osy/XG_Mobile_Station/Models/MX25L8006EM1I-12G.step

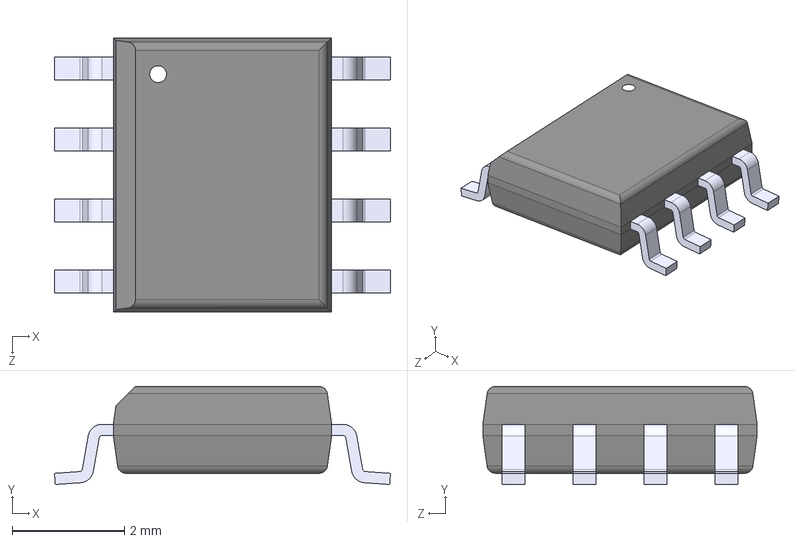
[picture p19: CAD file, 2024-03-20]
Models/MX25L8006EM1I-12G.step
6.00 x 1.75 x 4.90 mm
