osy/XG_Mobile_Station/Models/SN75LVPE4410RNQR.stp

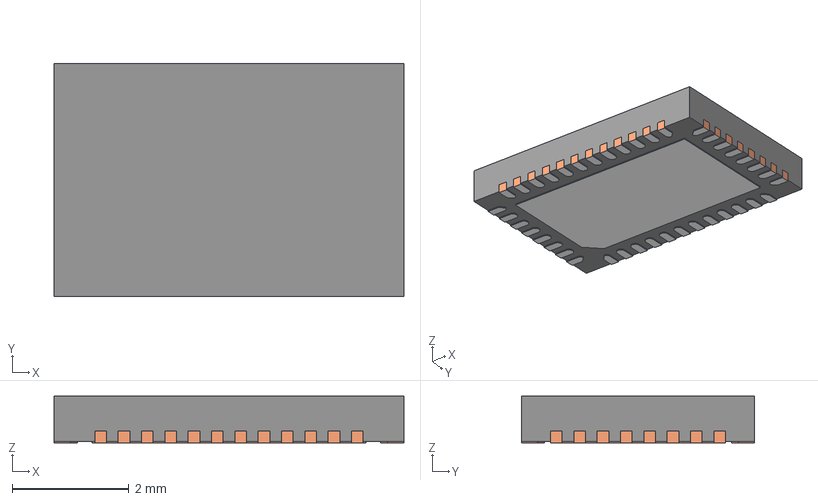
[picture p20: CAD file, 2024-03-20]
Models/SN75LVPE4410RNQR.stp
6.00 x 4.00 x 0.8 mm
BODY-QFN
FRAME-RNQ0040A
PIN1-ID
