osy/XG_Mobile_Station/Models/LM3489QMM-NOPB.stp

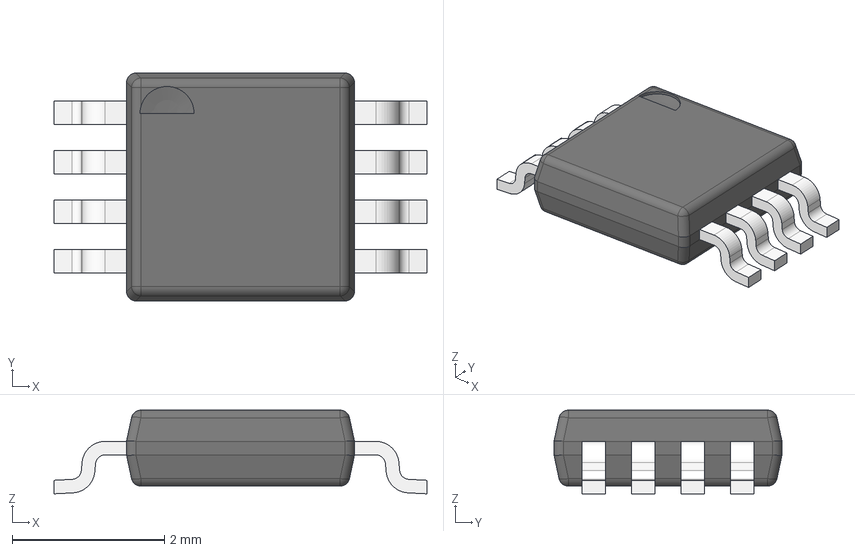
[picture p21: CAD file, 2024-03-20]
Models/LM3489QMM-NOPB.stp
4.90 x 3.00 x 1.10 mm
BODY_MUA08A
LEAD_MUA08A x 8
