osy/XG_Mobile_Station/Models/AON7403.step

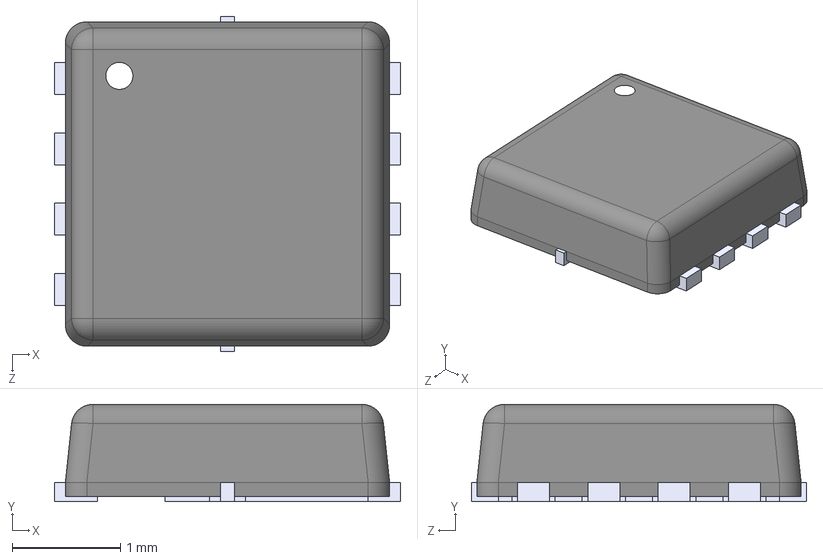
[picture p22: CAD file, 2024-03-20]
Models/AON7403.step
3.20 x 0.9 x 3.10 mm
