osy/XG_Mobile_Station/Models/LM3478MA-NOPB.stp

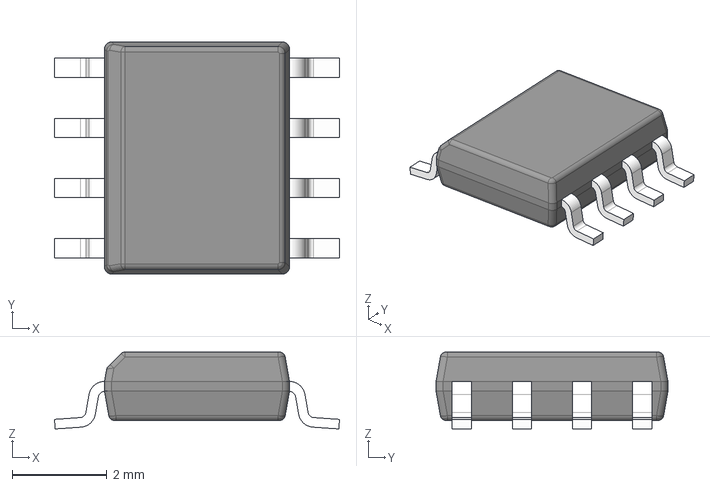
[picture p23: CAD file, 2024-03-20]
Models/LM3478MA-NOPB.stp
6.02 x 4.90 x 1.63 mm
BODY-SO
LEAD-D0008A x 8
