osy/XG_Mobile_Station/XGMDriver/devinstall/devinstall.h

/*++

Copyright (c) Microsoft Corporation.  All rights reserved.

Module Name:

    devcon.h

Abstract:

    Device Console header

--*/

#include <windows.h>
#include <tchar.h>
#include <stdlib.h>
#include <stdio.h>
#include <setupapi.h>
#include <regstr.h>
#include <infstr.h>
#include <cfgmgr32.h>
#include <string.h>
#include <malloc.h>
#include <newdev.h>
#include <objbase.h>
#include <strsafe.h>
#include <io.h>
#include <fcntl.h>

#include "msg.h"
#include "rc_ids.h"

#ifndef ARRAYSIZE
#define ARRAYSIZE(a)                (sizeof(a)/sizeof(a[0]))
#endif

typedef int (*DispatchFunc)(_In_ LPCTSTR BaseName, _In_opt_ LPCTSTR Machine, _In_ DWORD Flags, _In_ int argc, _In_ LPTSTR argv[]);
typedef int (*CallbackFunc)(_In_ HDEVINFO Devs, _In_ PSP_DEVINFO_DATA DevInfo, _In_ DWORD Index, _In_ LPVOID Context);

typedef struct {
    LPCTSTR         cmd;
    DispatchFunc    func;
    DWORD           shortHelp;
    DWORD           longHelp;
} DispatchEntry;

extern DispatchEntry DispatchTable[];

#ifndef ARRAYSIZE
#define ARRAYSIZE(x) (sizeof(x)/sizeof(x[0]))
#endif

#define INSTANCEID_PREFIX_CHAR TEXT('@') // character used to prefix instance ID's
#define CLASS_PREFIX_CHAR      TEXT('=') // character used to prefix class name
#define WILD_CHAR              TEXT('*') // wild character
#define QUOTE_PREFIX_CHAR      TEXT('\'') // prefix character to ignore wild characters
#define SPLIT_COMMAND_SEP      TEXT(":=") // whole word, indicates end of id's

//
// Devcon.exe command line flags
//
#define DEVCON_FLAG_FORCE       0x00000001

void FormatToStream(_In_ FILE* stream, _In_ DWORD fmt, ...);
int EnumerateDevices(_In_ LPCTSTR BaseName, _In_opt_ LPCTSTR Machine, _In_ DWORD Flags, _In_ int argc, _In_reads_(argc) PWSTR* argv, _In_ CallbackFunc Callback, _In_ LPVOID Context);
__drv_allocatesMem(object) LPTSTR* GetDevMultiSz(_In_ HDEVINFO Devs, _In_ PSP_DEVINFO_DATA DevInfo, _In_ DWORD Prop);
__drv_allocatesMem(object) LPTSTR* GetMultiSzIndexArray(_In_ __drv_aliasesMem LPTSTR MultiSz);
void DelMultiSz(_In_opt_ __drv_freesMem(object) PZPWSTR Array);
__drv_allocatesMem(object) LPTSTR* CopyMultiSz(_In_opt_ PZPWSTR Array);

BOOL Reboot();


//
// UpdateDriverForPlugAndPlayDevices
//
typedef BOOL(WINAPI* UpdateDriverForPlugAndPlayDevicesProto)(_In_opt_ HWND hwndParent,
    _In_ LPCTSTR HardwareId,
    _In_ LPCTSTR FullInfPath,
    _In_ DWORD InstallFlags,
    _Out_opt_ PBOOL bRebootRequired
    );
typedef BOOL(WINAPI* SetupSetNonInteractiveModeProto)(_In_ BOOL NonInteractiveFlag
    );
typedef BOOL(WINAPI* SetupUninstallOEMInfProto)(_In_ LPCTSTR InfFileName,
    _In_ DWORD Flags,
    _Reserved_ PVOID Reserved
    );

#if _SETUPAPI_VER >= _WIN32_WINNT_WINXP
typedef BOOL(WINAPI* SetupVerifyInfFileProto)(_In_ LPCTSTR InfName,
    _In_opt_ PSP_ALTPLATFORM_INFO_V2 AltPlatformInfo,
    _Inout_ PSP_INF_SIGNER_INFO InfSignerInfo);
#endif

#ifdef _UNICODE
#define UPDATEDRIVERFORPLUGANDPLAYDEVICES "UpdateDriverForPlugAndPlayDevicesW"
#define SETUPUNINSTALLOEMINF "SetupUninstallOEMInfW"
#else
#define UPDATEDRIVERFORPLUGANDPLAYDEVICES "UpdateDriverForPlugAndPlayDevicesA"
#define SETUPUNINSTALLOEMINF "SetupUninstallOEMInfA"
#endif
#define SETUPSETNONINTERACTIVEMODE "SetupSetNonInteractiveMode"
#define SETUPVERIFYINFFILE "SetupVerifyInfFile"

//
// exit codes
//
#define EXIT_OK      (0)
#define EXIT_REBOOT  (1)
#define EXIT_FAIL    (2)
#define EXIT_USAGE   (3)
